wyolum/hack_PGH_badge/3D_2D_assets/image1.png

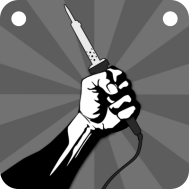
3D_2D_assets/image1.png
