wyolum/hack_PGH_badge/kicad/Library_3D_CAD_models/D_DO-34_SOD68_P7.62mm_Horizontal.step

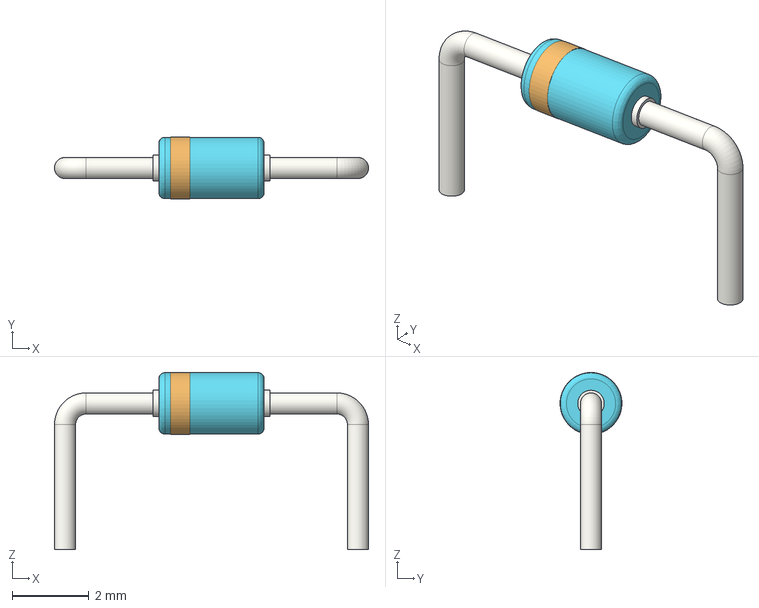
[picture p22: CAD file, 2024-12-01]
kicad/Library_3D_CAD_models/D_DO-34_SOD68_P7.62mm_Horizontal.step
8.17 x 1.61 x 4.61 mm
