wyolum/hack_PGH_badge/3D_2D_assets/hackPGH_logo_01.dxf

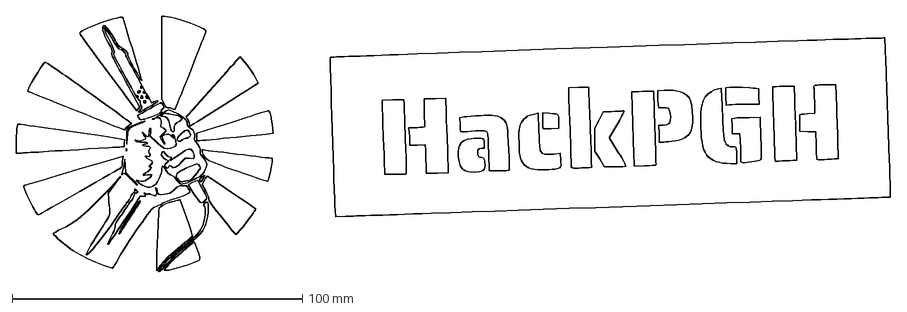
[picture p23: CAD file, 2024-12-01]
3D_2D_assets/hackPGH_logo_01.dxf
301.5 x 88.0 mm
